adct-the-experimenter/read-rope/ltspice-sim-with-load.asc

R_Load_ADC: res; 100Meg
Req: res; {X}
Rtrack: res; 20k
VCC: voltage; 5
Named nets: 0, vout
.step param X 1k 20k 1k
.op
Resistors of Req include combinations of 750k,1Meg,2Meg,3Meg in prototype version 1.
Notes:
Load resistor is recommended to be at least 1 Meg.
Resistors of Req include combinations of 1k,10k,50k,100k in prototype version 1.1.
Goal is to get a linear relationship between output voltage and Req. This way it voltage can increase  linearly with increasing resistance.
Prototype version 1.2
Changes were made to account for using an ADC of a microcontroller such as atmega328p of Arduino Uno.
Prototype version 1.1
Prototype Version 1.0
Input impedance of ADC of atmega328p is 100 Meg.
ADC is optimized for signals with impedance of 10k ohms or less due to charging capacitor for sampling.
Larger resistances slow down the sampling time of ADC circuit.
Therefore, the circuit was changed. 100Meg load. 20k ohms total Req of all combinations. Rtrack is 20k ohms.
Resistor combinations changed to 1k,3k,7k,9k.
Max output impedance, ignoring load since it is the ADC,  is 10k when Req is 20k.
Input voltage VCC was changed to 5V so that it could use power from microcontroller. 9V will work too.
