adct-the-experimenter/read-rope/ltspice-sim-results.png

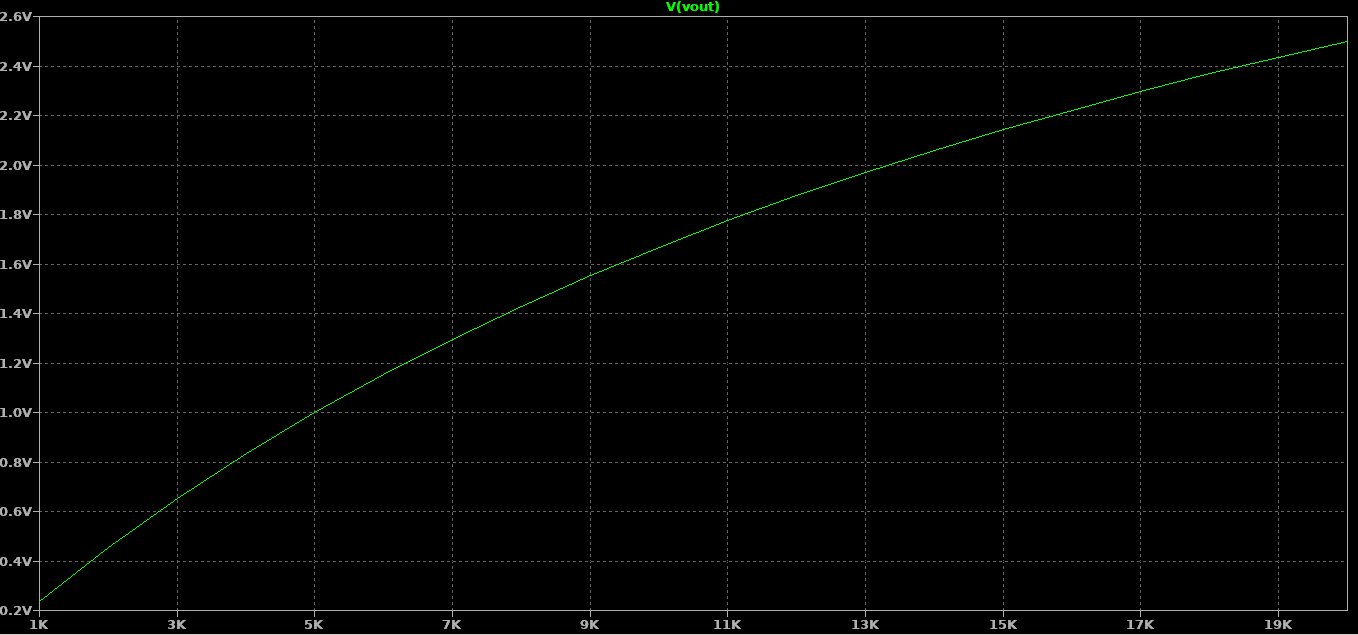
ltspice-sim-results.png
